meltoner/NEM_UAVRC_LEONARDO/UVRC_5/Steer.h

/*
  Steer.h - Library for wraping the functions controling Steer
  Created Konstantinos Papageorgiou  
*/

#ifndef Steer_h
#define Steer_h

#include "Arduino.h"
#include <Servo.h>
#include "Context.h"

class Steer{
  public:
    Steer(byte pin);
    void setup(Context &_context);
    void apply();
    void setSteer(int value);
    int getHeadingDifference();
    //boolean hasNewDegree();
    int center = 86;

  private:
    byte _pin;
    boolean on = false;
    Servo steer;
    unsigned long applied = 0;
    Context *context;
};

#endif
